paletiIndraneel/Sentinel/include/NotificationQueue.h

#pragma once

#include <Arduino.h>
#include <deque>

enum class NotificationLevel
{
    Info,
    Success,
    Warning,
    Error,
    Critical
};

struct NotificationRecord
{
    String timestamp;
    NotificationLevel level;
    String message;
    bool delivered;
};

class NotificationQueue
{
public:
    NotificationQueue();
    void enqueue(const NotificationRecord& notification);
    bool hasPending() const;
    const NotificationRecord& front() const;
    void dequeue();
    size_t size() const;
    void clear();

private:
    std::deque<NotificationRecord> queue_;
};
